benpeart/kaleidoscope/src/modes.cpp

#include "main.h"
#include "debug.h"
#include "settings.h"
#include "modes.h"

#include "Kaleidoscope.h"
#ifdef DEMO
#include "plasma.h"
#include "ripples.h"
#include "TwinkleFox.h"
#include "XYDistortionWaves.h"
#include "XYAALines.h"
#include "XYmatrix.h"
#include "XYpacifica.h"
#include "XYsnake.h"
#include "XYfire.h"
#endif

#ifdef TIME
#include "RealTimeClock.h"
#endif // TIME

// Calls to setMode() can happen asynchronously from the main loop, so we need to make sure that we don't
// try to draw a new mode until the previous mode has finished drawing. This flag is set to true when we
// enter a new mode and cleared when the first draw() call for that mode is complete.
bool eraseLEDs = true;

// This look up table lists each of the display/animation drawing functions
// (which appear later in this code) in the order they're selected with
// the right button.  Some functions appear repeatedly...for example,
// we return to "mode_off" at several points in the sequence.
KaleidoscopeMode KaleidoscopeModeLUT[]{
    {mode_kaleidoscope, "Kaleidoscope", true, {0, 0}},
#ifndef WIFI // if we have WIFI, we don't need the manual settings modes
#ifdef ENCODER
    {mode_off, "off", false, {0, 0}}, // make it obvious we're entering 'setup' modes
    {mode_kaleidoscope_select_speed_brightness, "kaleidoscope_select_speed_brightness", false, {0, 0}},
    //  { mode_kaleidoscope_select_disks, "mode_kaleidoscope_select_disks", false, {0, 0}},
    {mode_kaleidoscope_select_reflection_style, "mode_kaleidoscope_select_reflection_style", false, {0, 0}},
#ifdef TIME
    {mode_select_clock_face, "select_clock_face", false, {0, 0}},
#endif // TIME
#endif // ENCODER
#endif // WIFI
#ifdef DEMO
    {mode_kaleidoscope_plasma, "Plasma", true, {0, 0}},
    {mode_kaleidoscope_ripples, "Ripples", true, {0, 0}},
    {mode_kaleidoscope_twinkle_fox, "Twinkle Fox", true, {0, 0}},
    {mode_xy_aalines, "AA Lines", true, {0, 0}},
    {mode_xy_distortion_waves, "Distortion Waves", true, {0, 0}},
    {mode_xy_matrix, "Matrix", true, {0, 0}},
    {mode_xy_pacifica, "Pacifica", true, {0, 0}},
    {mode_xy_snake, "Snake", true, {0, 0}},
    {mode_xy_fire, "Fire", true, {0, 0}},
#endif
#ifdef DEBUG
    {mode_kaleidoscope_test, "kaleidoscope_test", true, {0, 0}},
    {mode_xy_test, "xy_test", true, {0, 0}},
    {mode_test, "test", true, {0, 0}},
#endif
    {mode_off, "off", false, {0, 0}} // make it obvious we're entering 'regular' modes
};
uint8_t kaleidoscopeModes = (sizeof(KaleidoscopeModeLUT) / sizeof(KaleidoscopeModeLUT[0])); // total number of valid modes in table

#ifdef ENCODER
// We need to save/restore the count for the rotary encoders
// when we switch between modes so that each mode doesn't impact
// the other modes.
#define LEFT_ENCODER 0
#define RIGHT_ENCODER 1
#endif // ENCODER

void setKaleidoscopeMode(int newMode)
{
    // if the mode changed
    if (settings.mode != newMode)
    {
#ifdef ENCODER
        int old_mode = settings.mode;

        // save the encoder count for the old mode and restore the new mode count
        KaleidoscopeModeLUT[old_mode].modeEncoderCounts[LEFT_ENCODER] = knobLeft.getCount();
        knobLeft.setCount(KaleidoscopeModeLUT[newMode].modeEncoderCounts[LEFT_ENCODER]);
        KaleidoscopeModeLUT[old_mode].modeEncoderCounts[RIGHT_ENCODER] = knobRight.getCount();
        knobRight.setCount(KaleidoscopeModeLUT[newMode].modeEncoderCounts[RIGHT_ENCODER]);
#endif

        // output the new mode name and set a flag to clear the led strips for the new mode
        DB_PRINTF("setKaleidoscopeMode: %s\r\n", KaleidoscopeModeLUT[settings.mode].modeName);
        settings.mode = newMode;
        eraseLEDs = true;
    }
}

void nextKaleidoscopeMode()
{
    // check for a mode change
    uint8_t newMode = settings.mode;

    if (newMode < (kaleidoscopeModes - 1))
        newMode++; // Advance to next mode
    else
        newMode = 0; // or "wrap around" to start

    setKaleidoscopeMode(newMode);
}

void previousKaleidoscopeMode()
{
    // check for a mode change
    uint8_t newMode = settings.mode;

    if (newMode)
        newMode--; // Go to prior mode
    else
        newMode = kaleidoscopeModes - 1; // or "wrap around" to last mode

    setKaleidoscopeMode(newMode);
}

// All Pixels off
void mode_off()
{
    // nothing to see here...
}
