benpeart/kaleidoscope/src/ripples.cpp

#include "main.h"
#include "settings.h"
#include "render.h"
#include "ripples.h"

#ifdef DEMO

#define DEFAULT_MILLIS 50
#define MIN_MILLIS 0
#define MAX_MILLIS (4 * DEFAULT_MILLIS)

static CRGBPalette16 currentPalette = OceanColors_p; // Use palettes instead of direct CHSV or CRGB assignments
static CRGBPalette16 targetPalette = OceanColors_p;  // Also support smooth palette transitioning

#define maxRipples 6 // Min is 2 and value has to be divisible by two because each ripple has a left and right component. This cuts down on bouncing code.

//----------------- Ripple structure definition ----------------------------------------------------------------

struct ripple
{ // Reko Meriö's structures

    // Local definitions

    // Persistent local variables

    // Temporary local variables
    uint8_t brightness; // 0 to 255
    int8_t color;       // 0 to 255
    int16_t pos;        // -1 to NUM_LEDS  (up to 127 LED's)
    int8_t velocity;    // 1 or -1
    uint8_t life;       // 0 to 20
    uint8_t maxLife;    // 10. If it's too long, it just goes on and on. . .
    uint8_t fade;       // 192
    bool exist;         // 0 to 1

    void Move()
    {

        pos += velocity;
        life++;

        if (pos > NUM_LEDS - 1)
        { // Bounce back from far end.
            velocity *= -1;
            pos = NUM_LEDS - 1;
        }

        if (pos < 0)
        { // Bounce back from 0.
            velocity *= -1;
            pos = 0;
        }

        brightness = scale8(brightness, fade); // Adjust brightness accordingly to strip length

        if (life > maxLife)
            exist = false; // Kill it once it's expired.

    } // Move()

    void Init(uint8_t Fade, uint8_t MaxLife)
    { // Typically 216, 20

        pos = random8(NUM_LEDS / 8, NUM_LEDS - NUM_LEDS / 8); // Avoid spawning too close to edge.
        velocity = 1;                                         // -1 or 1
        life = 0;                                             // 0 to Maxlife
        maxLife = MaxLife;                                    // 10 called
        exist = true;                                         // 0, 1
        brightness = 255;                                     // 0 to 255
        color = millis();                                     // hue;
        fade = Fade;                                          // 192 called

    } // Init()

}; // struct ripple

typedef struct ripple Ripple;

Ripple ripples[maxRipples];

void rippless()
{

    for (int i = 0; i < maxRipples; i += 2)
    { // Check to see if ripple has expired, and if so, create a new one.
        if (random8() > 224 && !ripples[i].exist)
        {                                  // Randomly create a new ripple if this one has expired.
            ripples[i].Init(192, 10);      // Initialize the ripple array with Fade and MaxLife values.
            ripples[i + 1] = ripples[i];   // Everything except velocity is the same for the ripple's other half. Position starts out the same for both halves.
            ripples[i + 1].velocity *= -1; // We want the other half of the ripple to go opposite direction.
        }
    }

    for (int i = 0; i < maxRipples; i++)
    { // Move the ripple if it exists
        if (ripples[i].exist)
        {
            drawPixel(leds, ripples[i].pos, ColorFromPalette(currentPalette, ripples[i].color, ripples[i].brightness, LINEARBLEND));
            //      leds[ripples[i].pos] = ColorFromPalette(currentPalette, ripples[i].color, ripples[i].brightness, LINEARBLEND);
            ripples[i].Move();
        }
    }

    fadeToBlackBy(leds, NUM_STRIPS * NUM_LEDS_PER_STRIP, 160);

} // rippless()

void SetupMySimilar4Palette()
{ // Create a palette with colours close to each other.

    uint8_t thishue = random8();

    targetPalette = CRGBPalette16(CHSV(thishue + random8(32), 255, random8(128, 255)),
                                  CHSV(thishue + random8(32), 255, random8(192, 255)),
                                  CHSV(thishue + random8(32), 192, random8(192, 255)),
                                  CHSV(thishue + random8(32), 255, random8(128, 255)));

} // SetupMySimilar4Palette()

void mode_kaleidoscope_ripples()
{
    EVERY_N_MILLISECONDS(50)
    { // Smooth palette transitioning runs continuously.
        uint8_t maxChanges = 24;
        nblendPaletteTowardPalette(currentPalette, targetPalette, maxChanges);
        leds_dirty = true;
    }

    EVERY_N_SECONDS(5)
    {
        SetupMySimilar4Palette(); // Change palette colours every 5 seconds.
        leds_dirty = true;
    }

    EVERY_N_MILLIS_I(timer, DEFAULT_MILLIS)
    {               // Sets the original delay time.
        timer.setPeriod(MAX_MILLIS - map(settings.speed, MIN_SPEED, MAX_SPEED, MIN_MILLIS, MAX_MILLIS));
        rippless(); // Run the ripple routine.
        leds_dirty = true;
    }

    adjustBrightness();
    adjustSpeed();
} // mode_kaleidoscope_ripples()

#endif
