benpeart/kaleidoscope/src/RealTimeClock.h

#ifndef REALTIMECLOCK_H
#define REALTIMECLOCK_H

#include "render.h"

// maximum lenth of a valid mode name
#define MAX_FACE_NAME 16

/// Data structure to represent each possible clock face.
struct ClockFace
{
    void (*renderFunc)(void);           // pointer to the function that will render the clock face
    const char faceName[MAX_FACE_NAME]; // name of the clock face to use in the UI and REST APIs
};

// This look up table lists each of the available modes.
extern ClockFace clockFaceLUT[];
extern uint8_t clockFaces; // Number of clock faces in the lookup table

int setClockFace(int newFace);
extern CRGB clockColor;

#ifndef WIFI // if we have WIFI, we don't need the manual settings modes
void mode_select_clock_face();
#endif

void rtc_setup();

#endif // REALTIMECLOCK_H
